seamansrl/CloudSign/Chasis/esquema.jpg

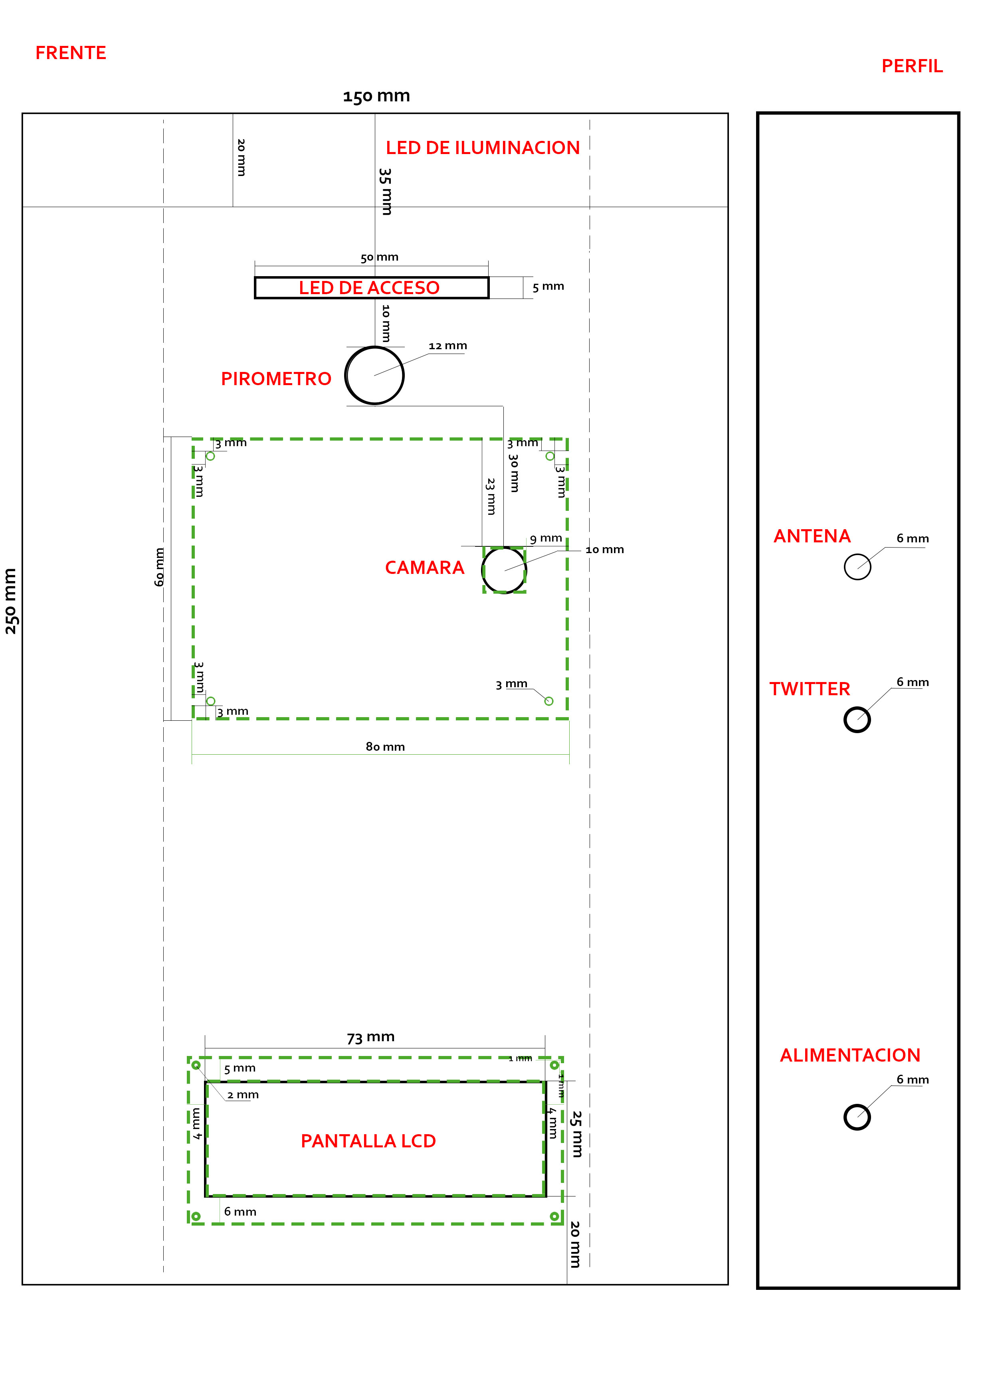
Chasis/esquema.jpg
