seamansrl/CloudSign/Manager/Resources/ayuda.png

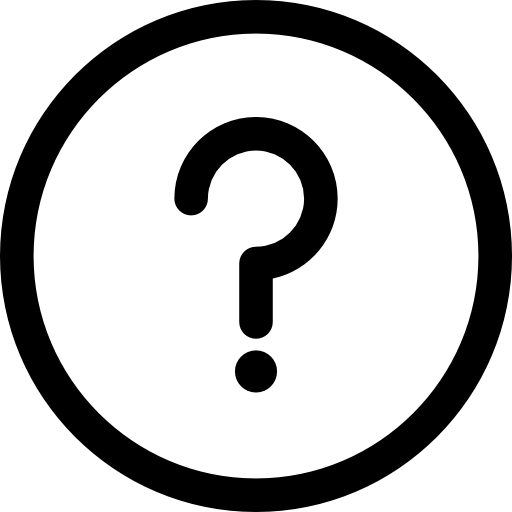
Manager/Resources/ayuda.png
