seamansrl/CloudSign/Manager/Resources/banking-security-biometrics.png

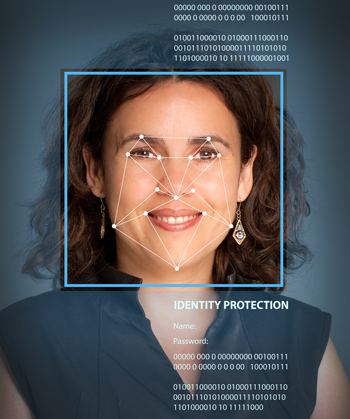
Manager/Resources/banking-security-biometrics.png
