seamansrl/CloudSign/Manager/Resources/Configuracion.jpg

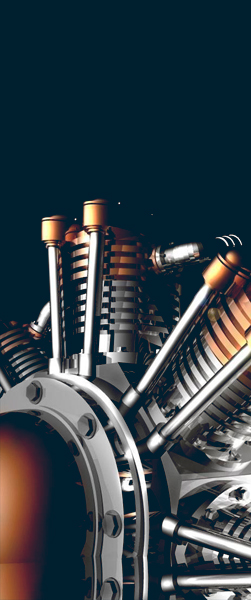
Manager/Resources/Configuracion.jpg
