seamansrl/CloudSign/Manager/Resources/Detecciones.jpg

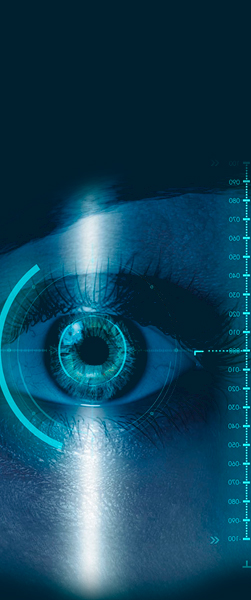
Manager/Resources/Detecciones.jpg
