seamansrl/CloudSign/Manager/Resources/Edificios.jpg

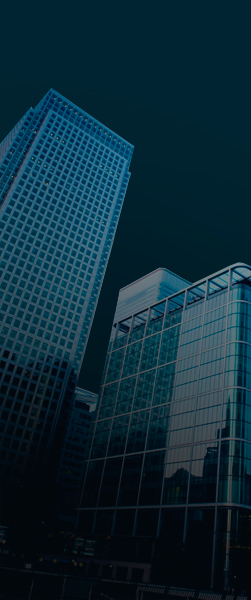
Manager/Resources/Edificios.jpg
