seamansrl/CloudSign/Manager/Resources/images.jpg

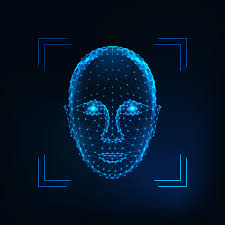
Manager/Resources/images.jpg
