seamansrl/CloudSign/PCB/HorusCamV3_etch_silk_bottom.pdf

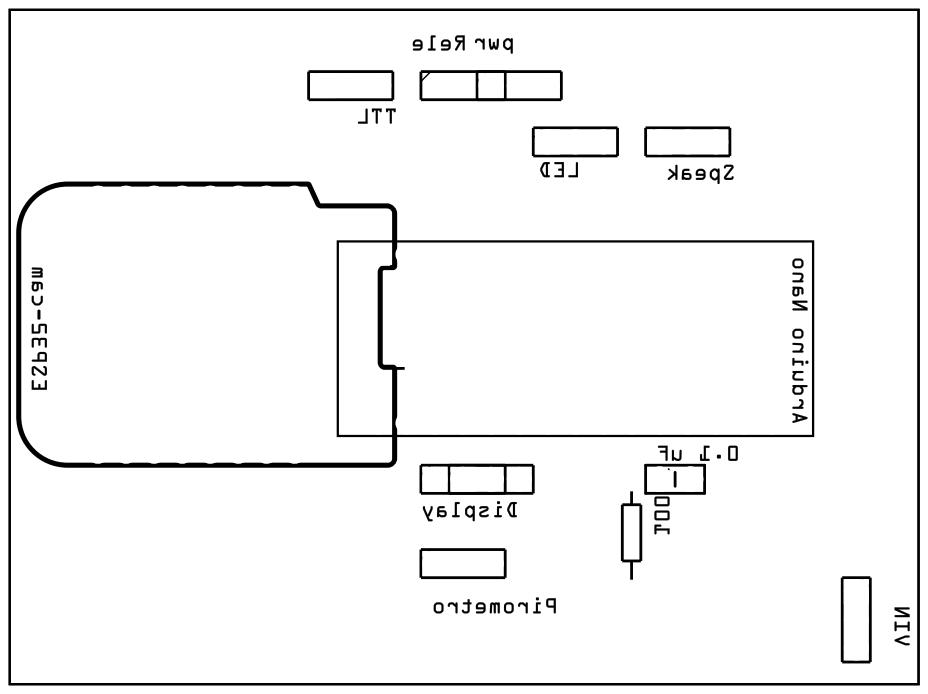
[picture p32: page 1]
