seamansrl/CloudSign/PCB/HorusCamV3_etch_silk_top.pdf

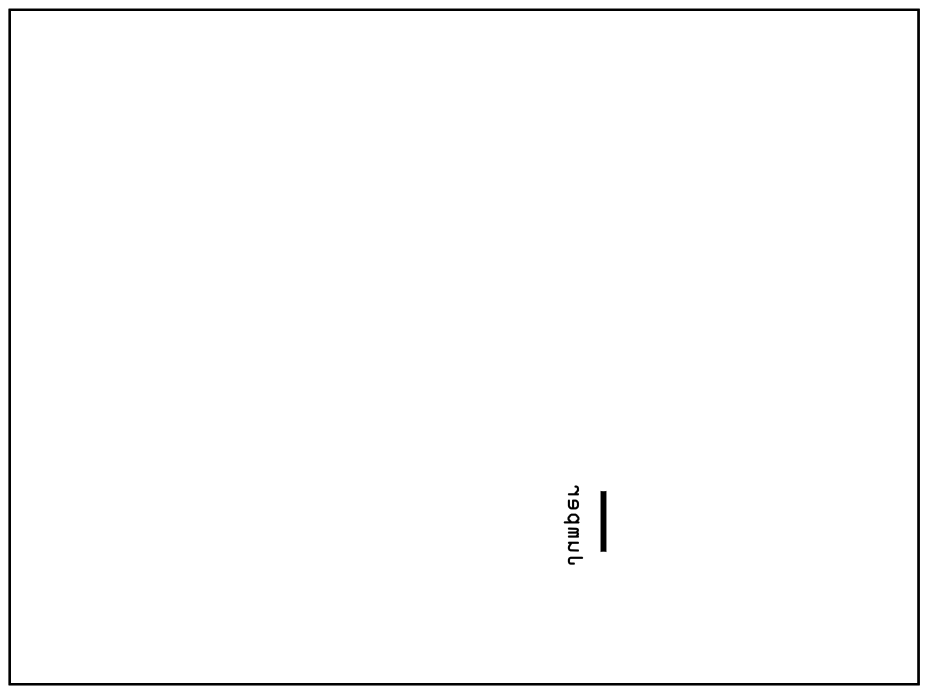
[picture p34: page 1]
